dcoberii/adjacent_reality_node/avr_src/l3g4200d.c

#include "l3g4200d.h"
#include "twi.h"

void l3g4200d_init(void){

	unsigned char buf[6];

	//We will set 5 contiguous ctrl registers located at CTRL_REG1
	buf[0] = L3G4200D_AUTO_INCREMENT | L3G4200D_CTRL_REG1;
	
	buf[1] = L3G4200D_DR_100HZ |	// Data rate
			 L3G4200D_PD |			// Power on
			 L3G4200D_ZEN |			// Z-Axis on
			 L3G4200D_YEN |			// Y-Axis on 	
			 L3G4200D_XEN;			// X-Axis on
	buf[2] = 0x00;					// CTRL_REG2
	buf[3] = L3G4200D_H_LACTIVE |	// Active low
			 L3G4200D_I2_DRDY;		// Enable DRDY interrupt pin on setting of ZYXDA (new data)
	buf[4] = L3G4200D_FS_2000DPS;	// Scale selection
	buf[5] = 0x00;					// CTRL_REG5
	
	twi_write_block(L3G4200D_ADDRESS, buf, 6);

}	

//Check for new data
unsigned char l3g4200d_drdy(void){

	//The data available bit of the status reg acts just like the DRDY interrupt pin
	//It is set when new data is available, and cleared once the 6 bytes have been read
	return twi_write_then_read_byte(L3G4200D_ADDRESS,L3G4200D_STATUS_REG) & L3G4200D_ZYXDA;

}

void l3g4200d_read(unsigned short *x,unsigned short *y, unsigned short *z){

	unsigned char buf[6];
	buf[0] =  L3G4200D_AUTO_INCREMENT | L3G4200D_OUT_X_L;
	twi_write_then_read_block(L3G4200D_ADDRESS,buf,1,buf, 6);

	*x = ((unsigned short)buf[1] << 8) + buf[0];
	*y = ((unsigned short)buf[3] << 8) + buf[2];
	*z = ((unsigned short)buf[5] << 8) + buf[4];

}
